mp035/shroom-puter/sw4stm32_workspace/climate_control/inc/print.h

void printchar(unsigned char value, unsigned char characters, unsigned char zeroleader);
void printshort(unsigned short value, unsigned char characters, unsigned char zeroleader);
void printlong(unsigned long value, unsigned char characters, unsigned char zeroleader);

void print_ram_string(char text[]);
void printstring(char *text);
extern void (*lcd_func)(unsigned char data);
